ArshSekhon/bkb-nice-nano-holder/pics/1.jpg

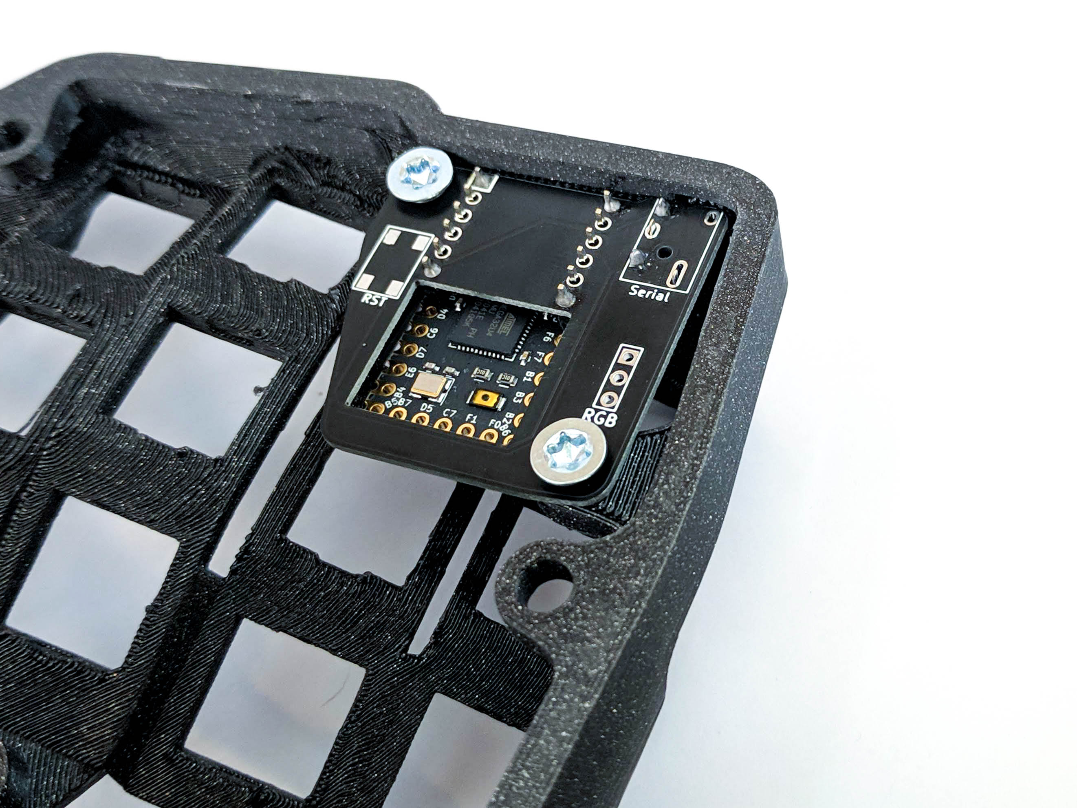
pics/1.jpg
