ArshSekhon/bkb-nice-nano-holder/pics/2.png

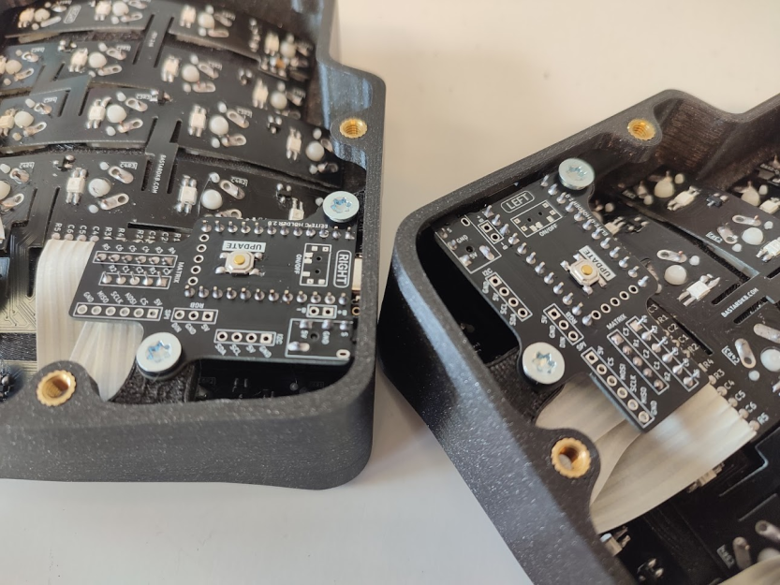
pics/2.png
